MBardehle/RC-Plane-Setup-Wizzard/Schaltpläne/Schaltplan.jpg

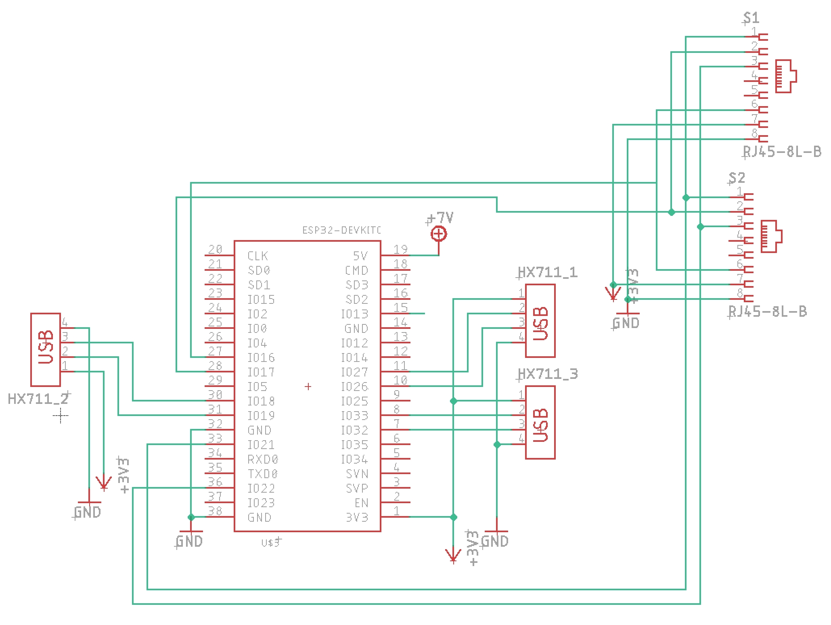
Schaltpläne/Schaltplan.jpg
